JRiggles/DELPHI-kbd/images/102 PCB Front.jpeg

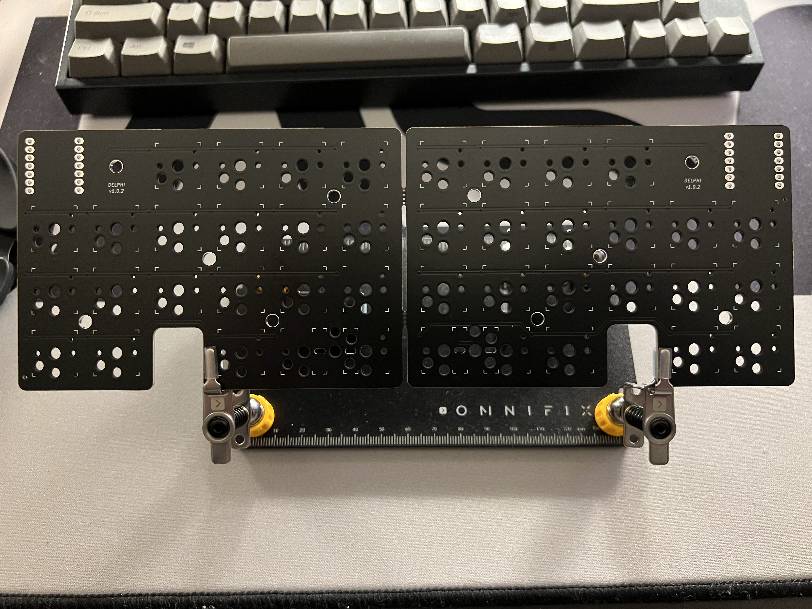
images/102 PCB Front.jpeg
