JRiggles/DELPHI-kbd/images/102 PCB Rear.jpg

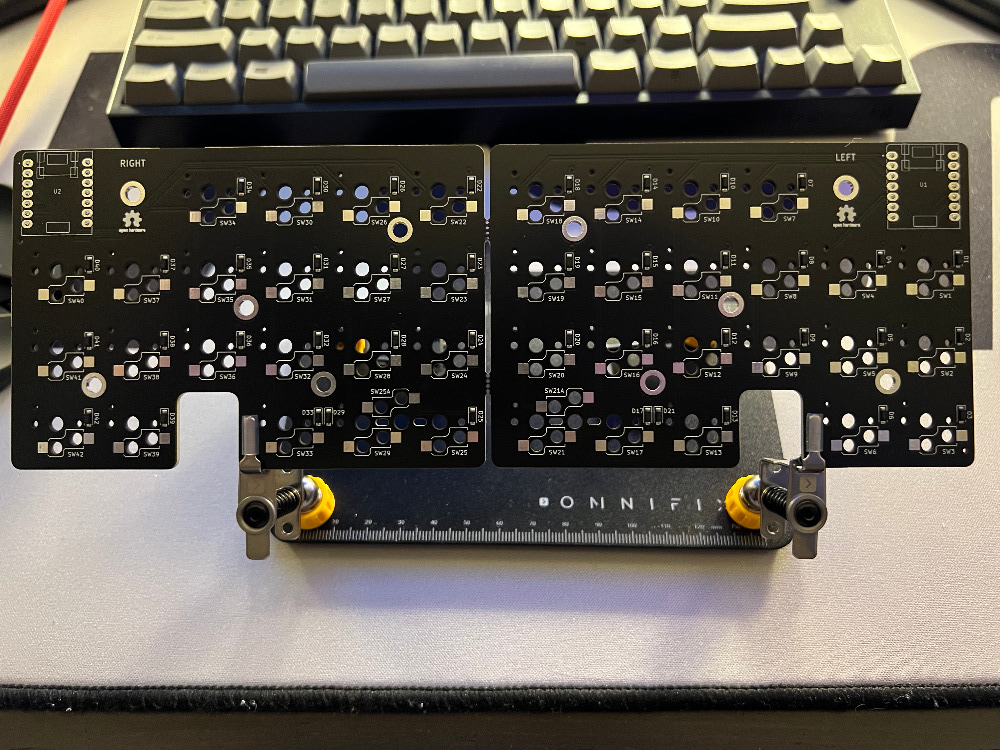
images/102 PCB Rear.jpg
