JRiggles/DELPHI-kbd/images/IMG_3724.jpeg

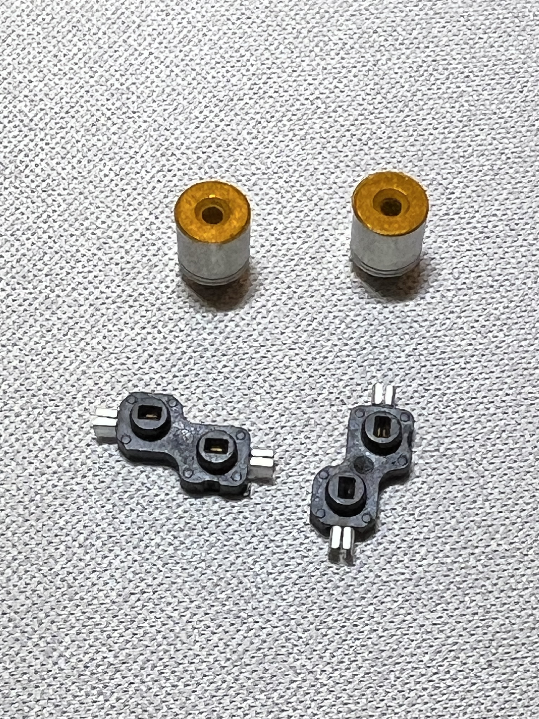
images/IMG_3724.jpeg
