JRiggles/DELPHI-kbd/images/IMG_3725.jpeg

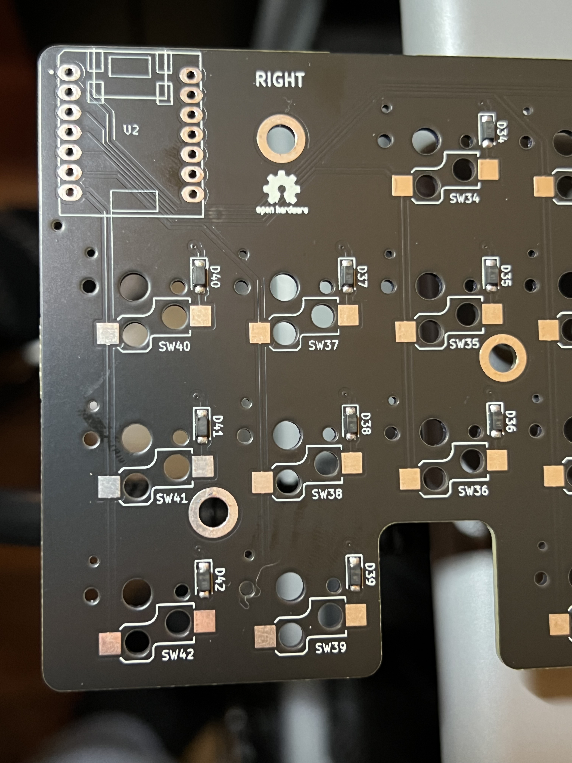
images/IMG_3725.jpeg
