JRiggles/DELPHI-kbd/images/IMG_3726.jpeg

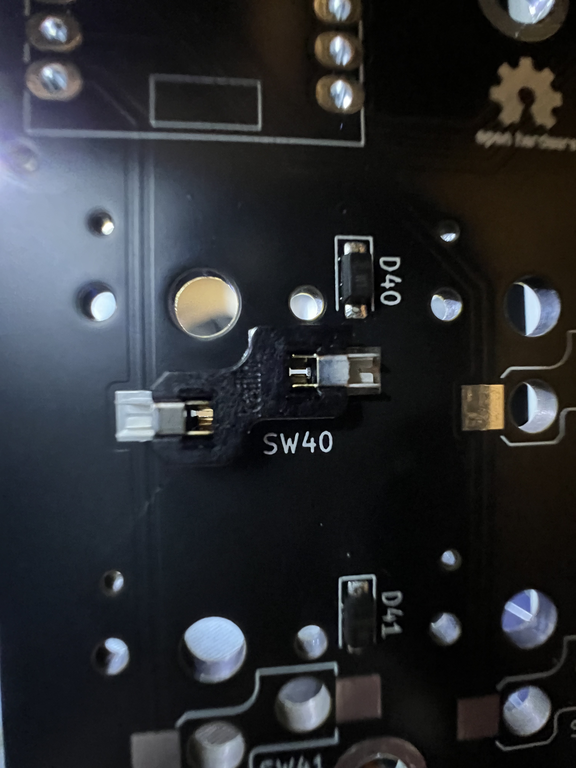
images/IMG_3726.jpeg
