JRiggles/DELPHI-kbd/images/IMG_3727.jpeg

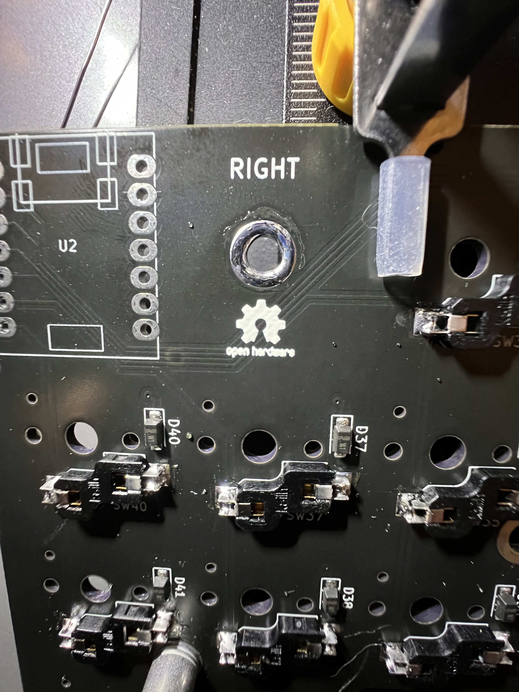
images/IMG_3727.jpeg
