JRiggles/DELPHI-kbd/images/IMG_3731.jpeg

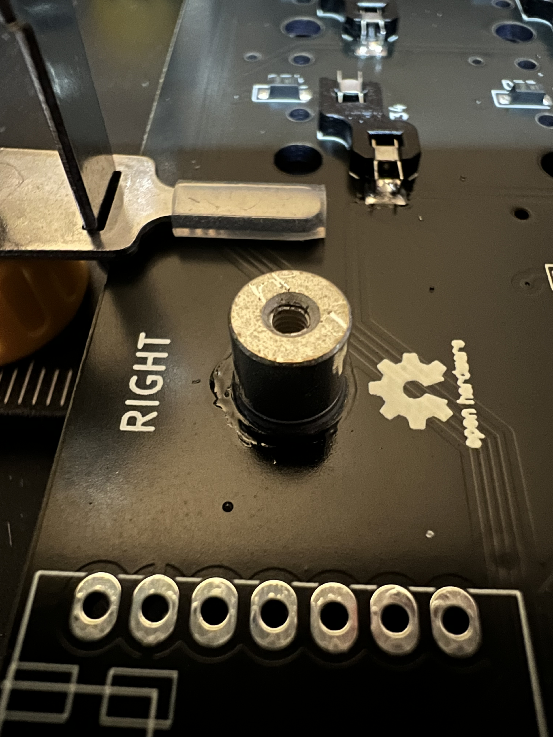
images/IMG_3731.jpeg
