JRiggles/DELPHI-kbd/images/IMG_3734.jpeg

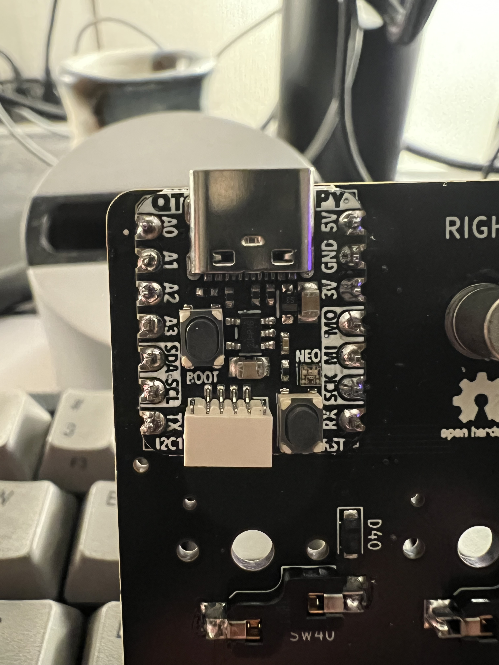
images/IMG_3734.jpeg
