JRiggles/DELPHI-kbd/images/IMG_3735.jpeg

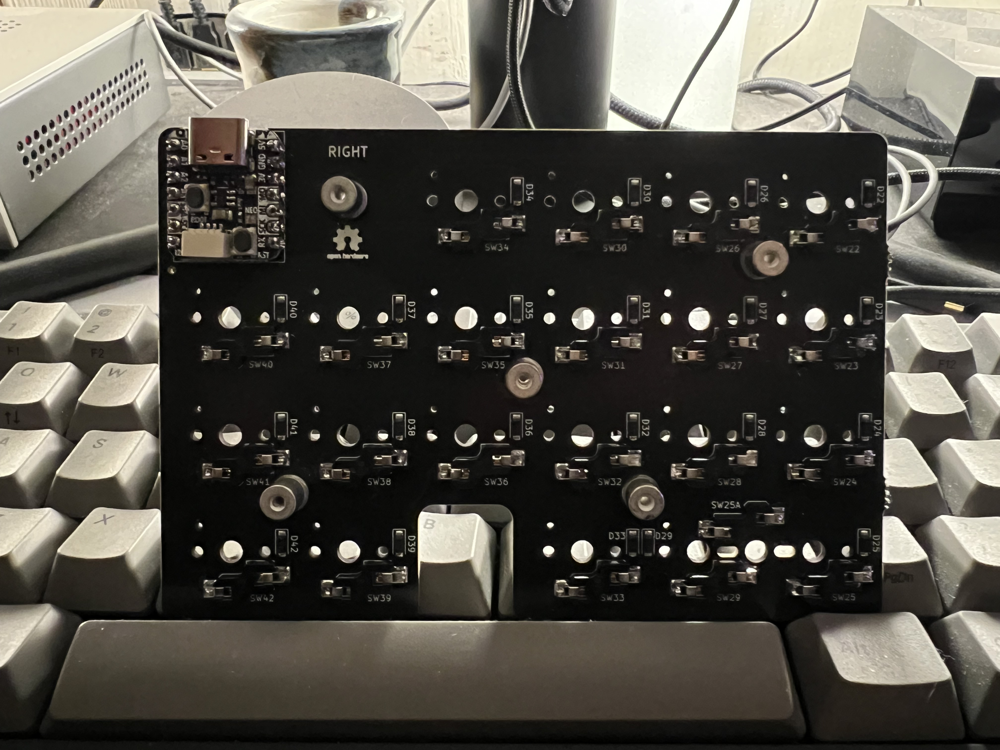
images/IMG_3735.jpeg
