JRiggles/DELPHI-kbd/images/IMG_3737.jpeg

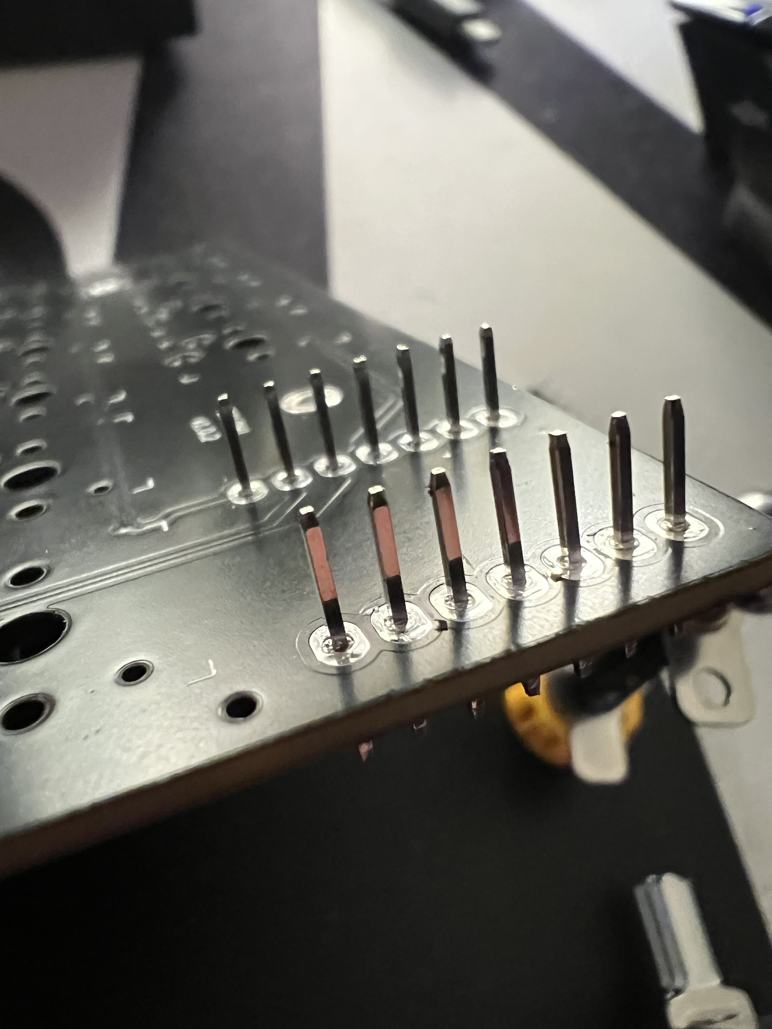
images/IMG_3737.jpeg
