JRiggles/DELPHI-kbd/images/IMG_3739.jpeg

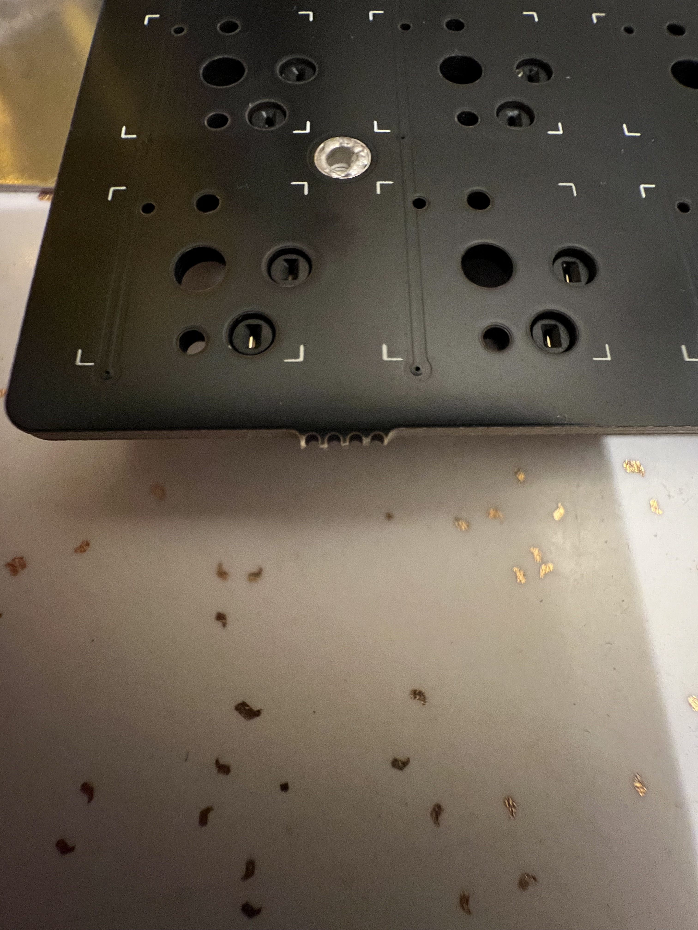
images/IMG_3739.jpeg
