JRiggles/DELPHI-kbd/images/IMG_3740.jpeg

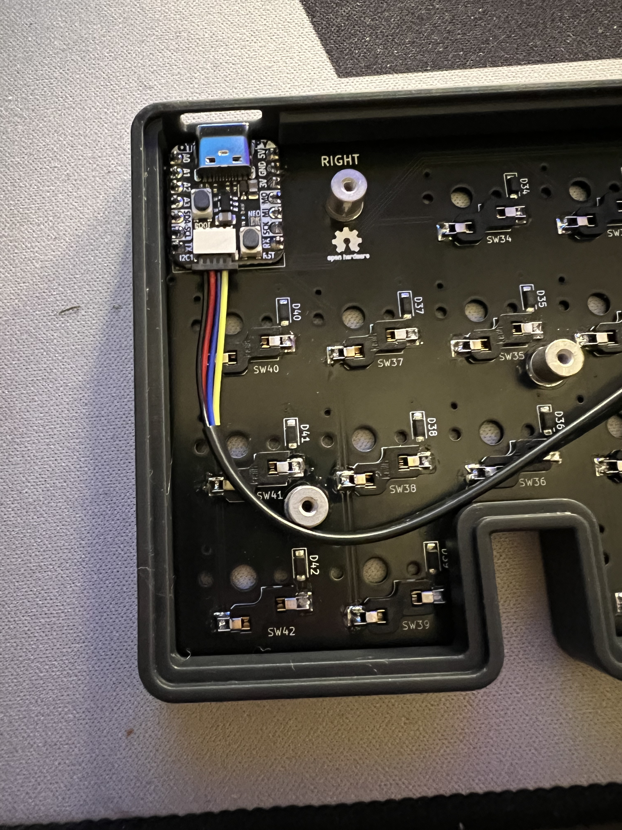
images/IMG_3740.jpeg
