JRiggles/DELPHI-kbd/images/IMG_3742.jpeg

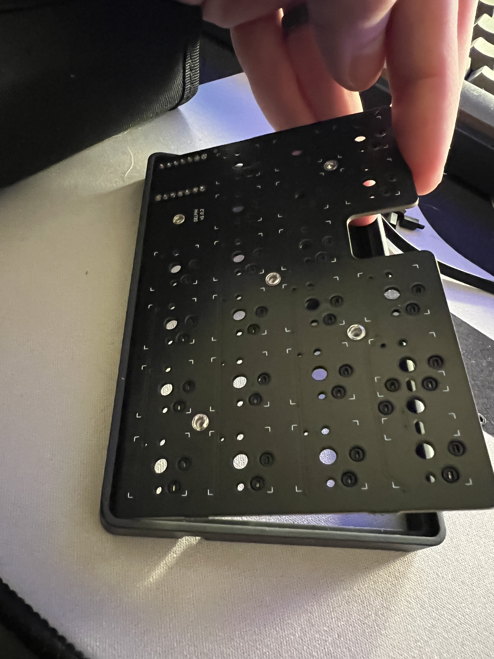
images/IMG_3742.jpeg
