JRiggles/DELPHI-kbd/images/IMG_3743.jpeg

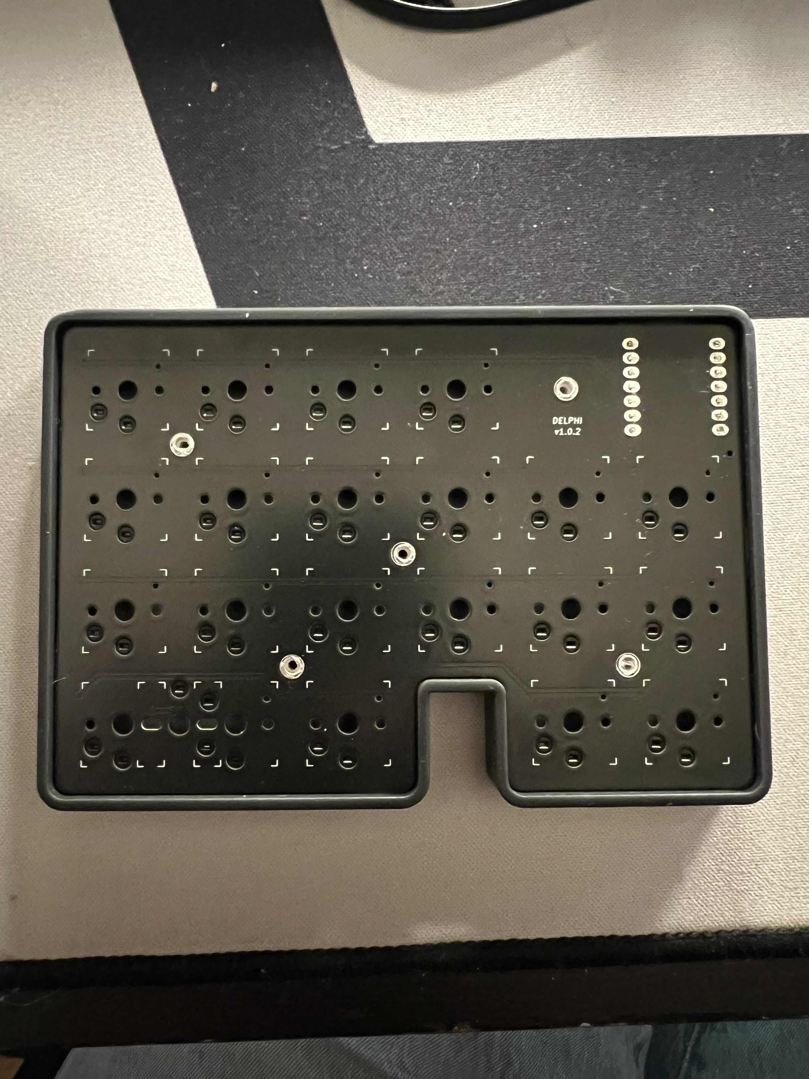
images/IMG_3743.jpeg
