JRiggles/DELPHI-kbd/images/IMG_3744.jpeg

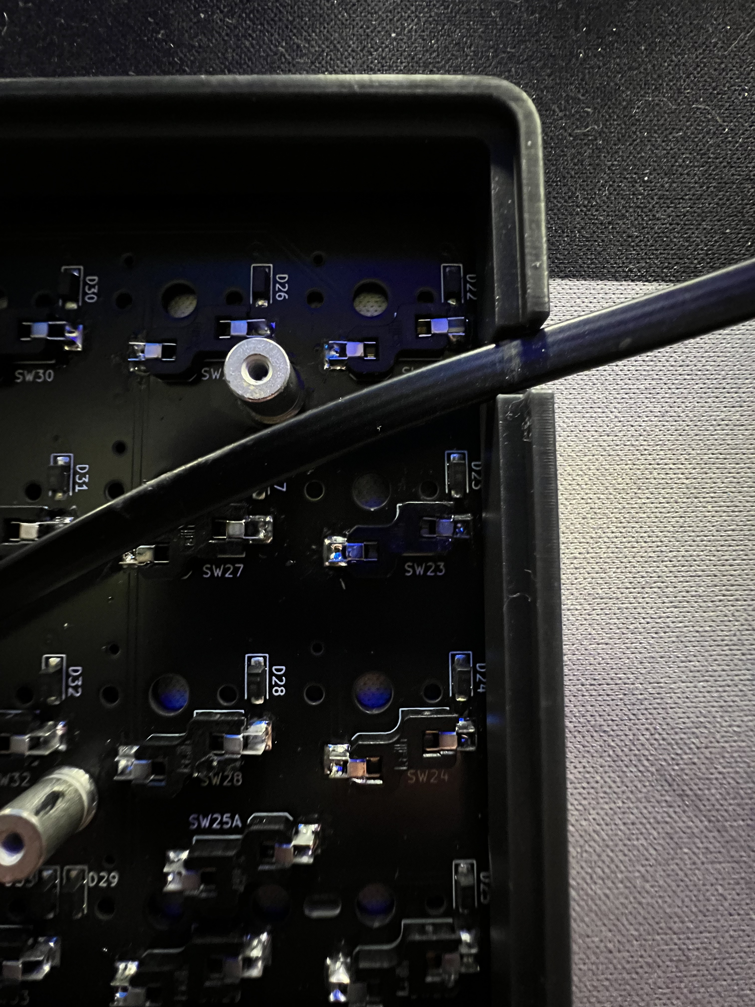
images/IMG_3744.jpeg
