JRiggles/DELPHI-kbd/images/IMG_3745.jpeg

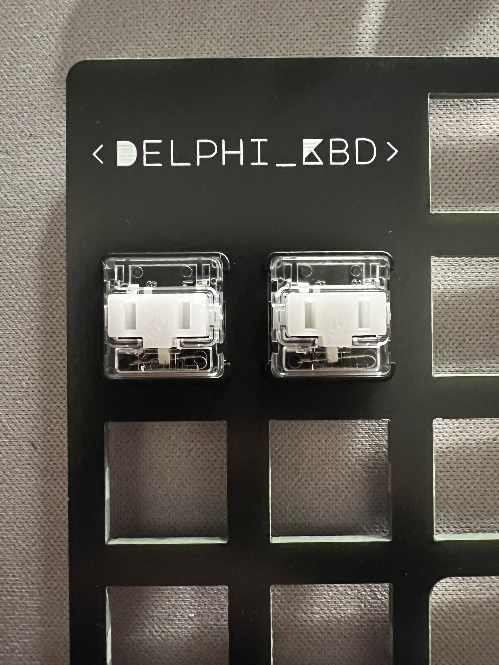
images/IMG_3745.jpeg
