JRiggles/DELPHI-kbd/images/IMG_3746.jpeg

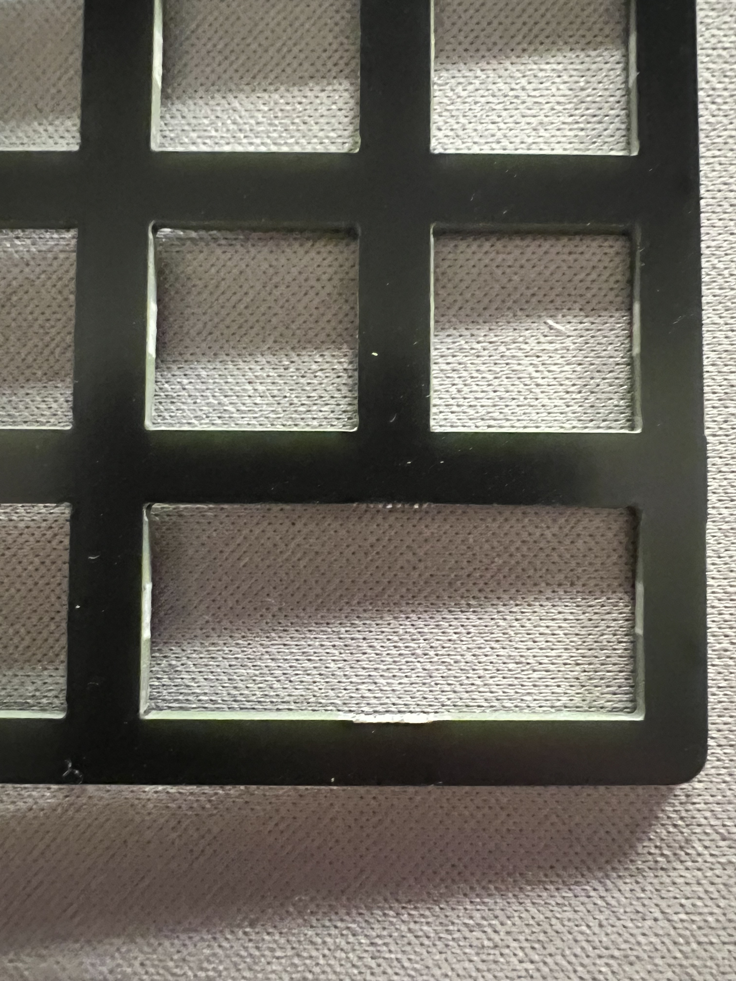
images/IMG_3746.jpeg
