JRiggles/DELPHI-kbd/images/IMG_3751.jpeg

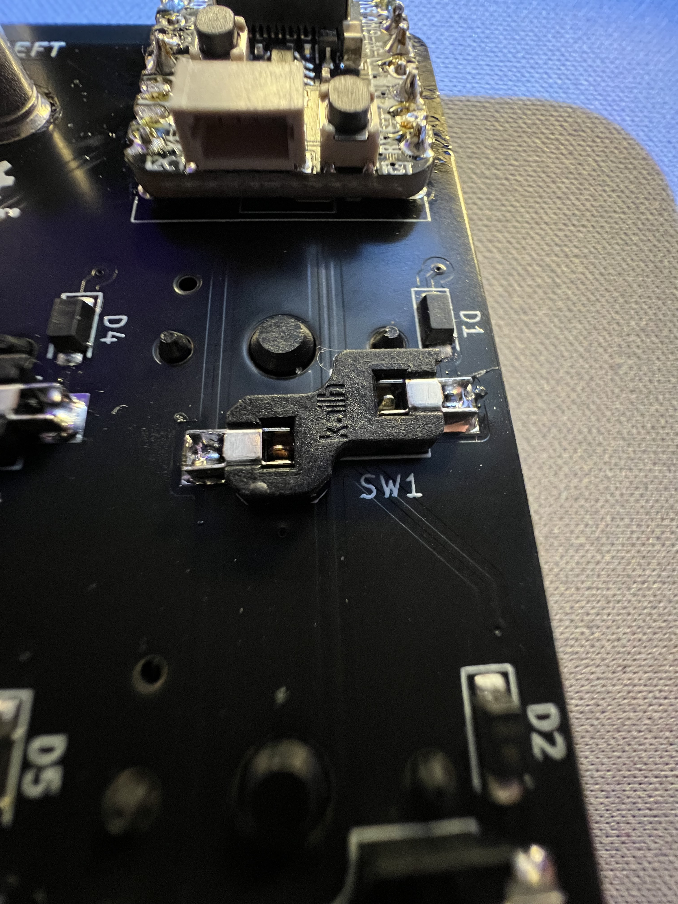
images/IMG_3751.jpeg
