JRiggles/DELPHI-kbd/images/IMG_3753.jpeg

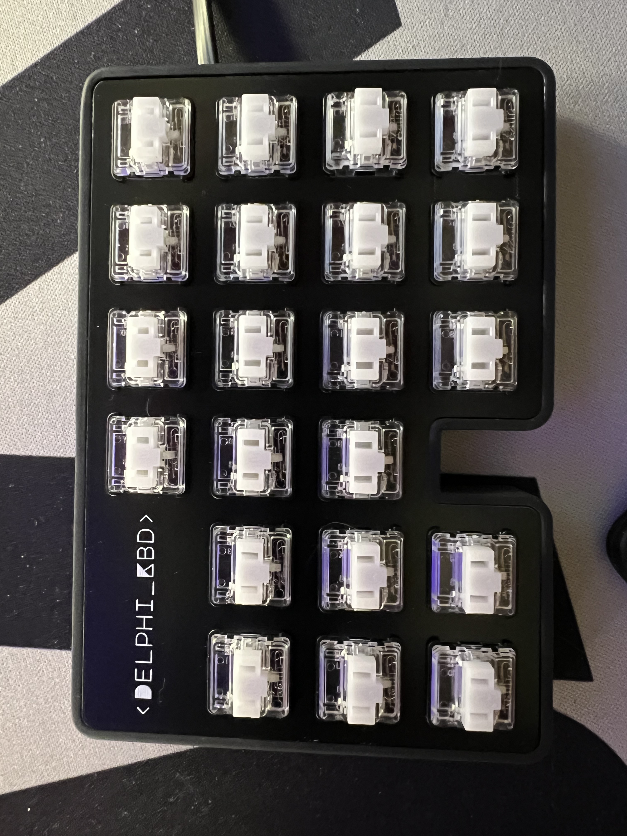
images/IMG_3753.jpeg
