JRiggles/DELPHI-kbd/images/IMG_3755.jpeg

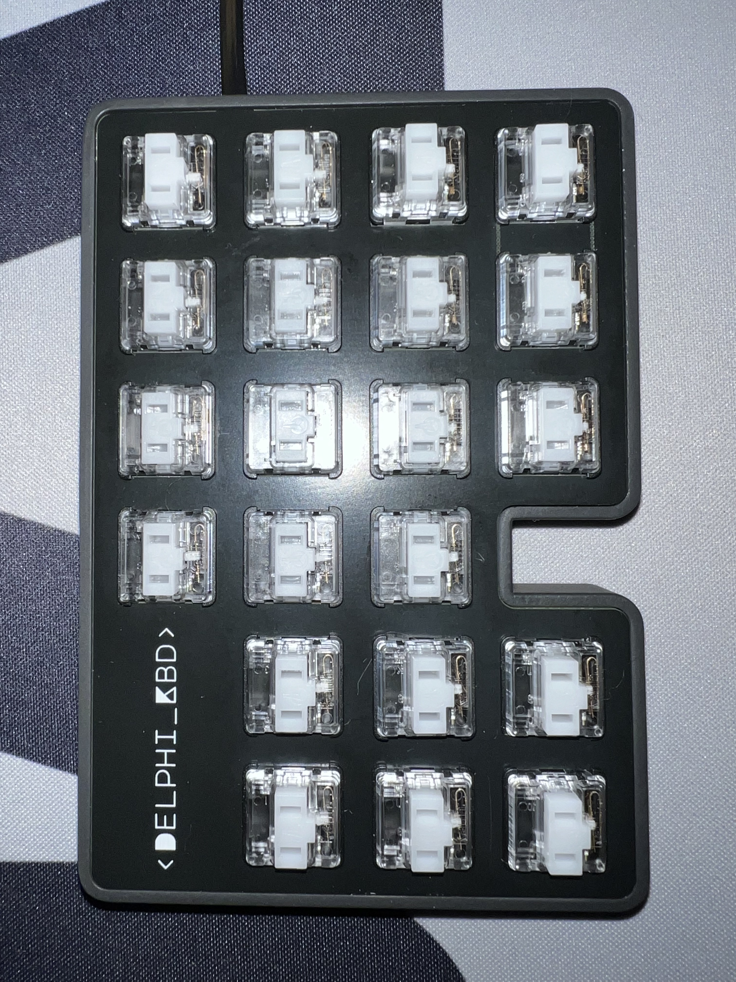
images/IMG_3755.jpeg
