JRiggles/DELPHI-kbd/images/IMG_3766.jpeg

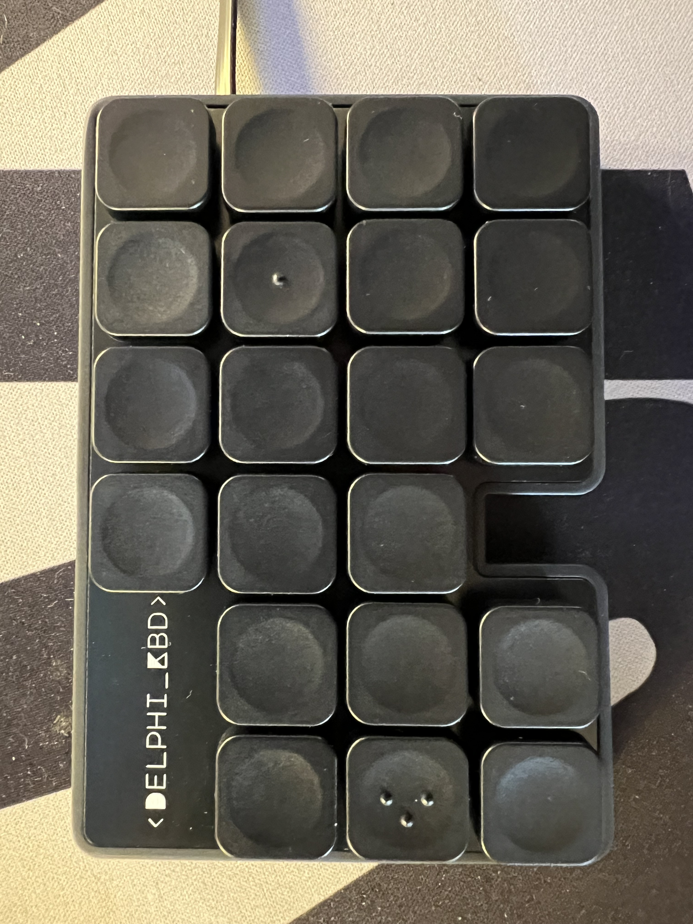
images/IMG_3766.jpeg
