JRiggles/DELPHI-kbd/images/IMG_3769.jpeg

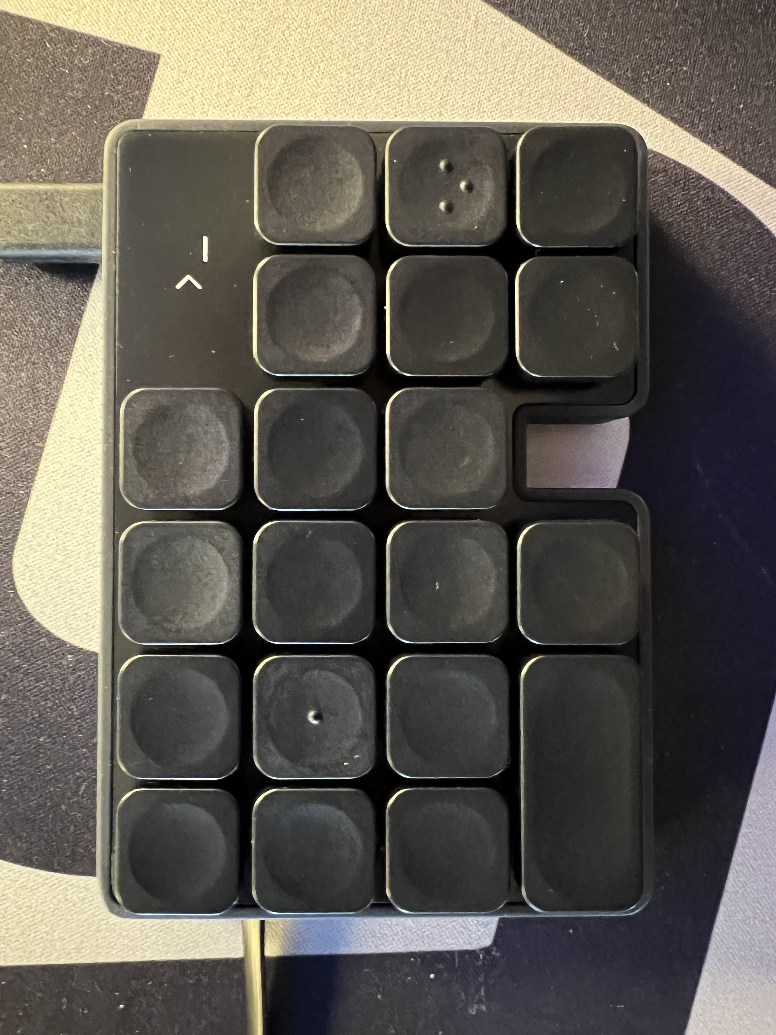
images/IMG_3769.jpeg
