JRiggles/DELPHI-kbd/images/Plates LEFT.jpeg

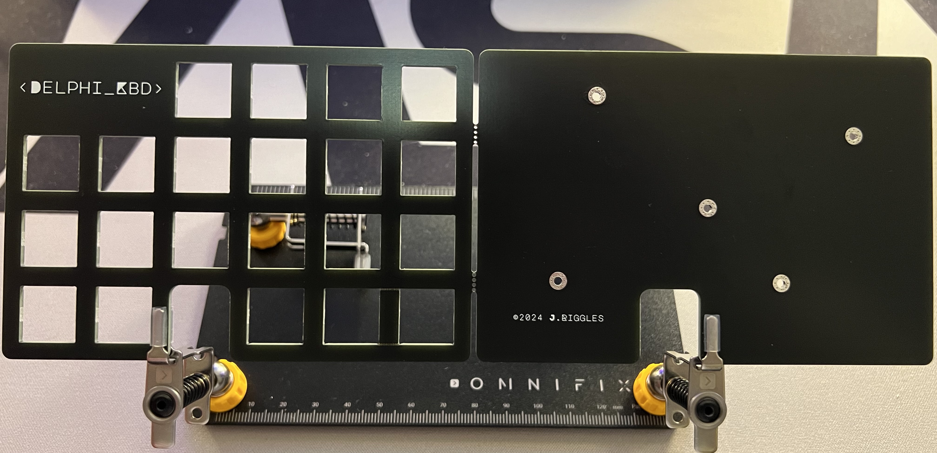
images/Plates LEFT.jpeg
