JRiggles/DELPHI-kbd/images/IMG_3750.jpeg

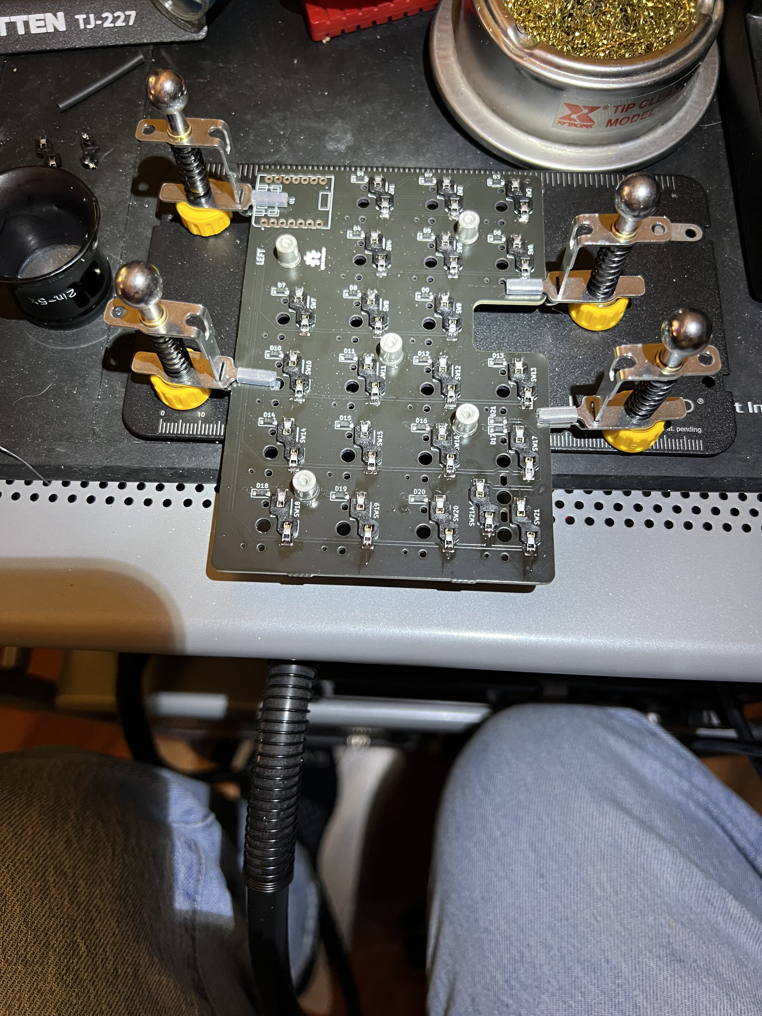
images/IMG_3750.jpeg
