JRiggles/DELPHI-kbd/images/IMG_3752.jpeg

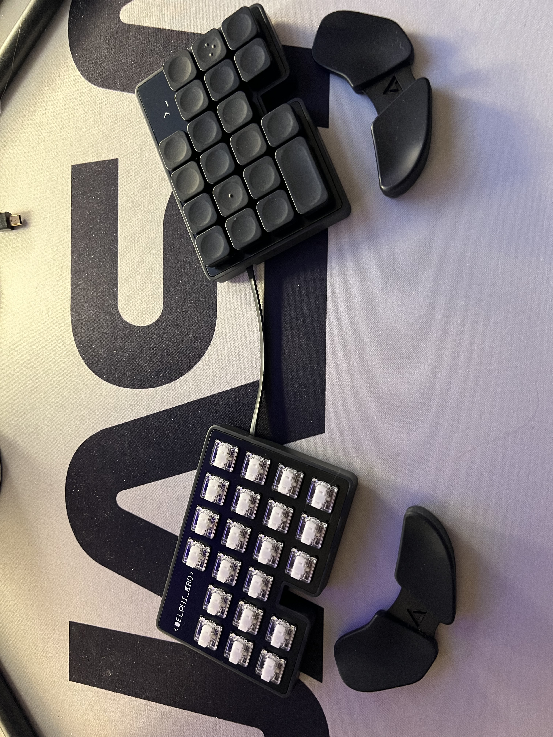
images/IMG_3752.jpeg
